kiryanenko/SmartParking-sensor/docs/Приложение Е. Графическая документация.pdf

# ПРИЛОЖЕНИЕ Е

# Графическая документация

# В графическую часть дипломного проекта входят:

1) Цели и задачи системы мониторинга парковочных мест (Рисунок Е.1);
2) Исследование | IoT | технологий | в | сфере | транспортной | инфраструктуры

(Рисунок Е.2);

3) Функциональная схема системы мониторинга парковочных мест (Рисунок Е.3);

# 4) Схема электрическая структурная МК-подсистемы регистрации свободных

парковочных мест (Рисунок Е.4);

# 5) Схема электрическая функциональная модуля контроля парковочного места

(Рисунок Е.5);

# 6) Схема электрическая функциональная МК-подсистемы регистрации свободных

парковочных мест (Рисунок Е.6);

# 7) Спецификация модуля контроля парковочного места на базе PCF8574P

(Рисунок Е.7);

# 8) Схема электрическая принципиальная модуля контроля парковочного места на

базе PCF8574P (Рисунок Е.8);

# 9) Спецификация модуля контроля парковочного места на базе PCF8574AP

(Рисунок Е.9);

# 10) Схема электрическая принципиальная модуля контроля парковочного места на

базе PCF8574AP (Рисунок Е.10);

# 11) Спецификация МК-подсистемы регистрации свободных парковочных мест

(Рисунки Е.11, Е.12);

# 12) Схема электрическая принципиальная МК-подсистемы регистрации свободных

парковочных мест (Рисунок Е.13);

# 13) Диаграмма классов МК-подсистемы регистрации свободных парковочных мест

(Рисунок Е.14);

14) Диаграмма классов вычислительного хаба (Рисунок Е.15);
15) Схема базы данных (Рисунок Е.16);
16) Алгоритм выдачи парковок (Рисунок Е.17);
17) Тестирование системы мониторинга парковочных мест (Рисунок Е.18).

Н.контроль Утв.

Изм. Лист | докум. | Подпись | Дата
Разраб. | Кирьяненко А.В.
Провер. | Попов А.Ю.
Т.контроль
Лит. | Масса | Масштаб
Лист | Листов

Система мониторинга парковочных мест

Цели и задачи

Выпускная квалификационная работа бакалавра

Реценз. | МГТУ им. Н.Э. Баумана группа ИУ6-81

# СИСТЕМА МОНИТОРИНГА ПАРКОВОЧНЫХ МЕСТ

Мобильное приложение | Веб-клиент

База
данных

### Сервер

API-сервисы

Вычислительный хаб | Вычислительный хаб

### МК-подсистема регистрации свободных парковочных мест

### МК-подсистема регистрации свободных парковочных мест

### МК-подсистема регистрации свободных парковочных мест

### МК-подсистема регистрации свободных парковочных мест

Пользователь

Просмотр на карте в режиме реального времени текущих состояний парковок

Фильтрация парковок

Бронирование и оплата парковки

Регистрация

Авторизация

Просмотр совершенных заказов

Бронирование и оплата парковки через терминал оплаты

Получение информации о состоянии парковок по табло индикации

Владелец стоянки

Добавление /
удаление датчика

Добавление / изменение / удаление стоянки

Добавление / изменение / удаление парковочного места

Просмотр совершенных заказов на парковки владельца

Настройка параметров датчика

ЦЕЛИ: Создание программно-аппаратного прототипа системы мониторинга парковочных мест для определения наличия свободных парковок и отображения этих данных пользователям в режиме реального времени.

# ЗАДАЧИ: -Исследование IoT технологий в сфере транспортной инфраструктуры

# -Анализ предметной области -Разработка архитектуры системы

# -Разработка МК-подсистемы регистрации свободных парковочных мест

# -Разработка программной части компонентов системы -Обеспечение качества и надёжности системы

# Рисунок Е.1 – Цели и задачи системы мониторинга парковочных мест

Утв.

Изм. Лист | докум. | Подпись | Дата
Разраб. | Кирьяненко А.В.
Провер. | Попов А.Ю.

Т.контроль

Н.контроль

Лит. | Масса | Масштаб
Лист | Листов

Система мониторинга парковочных мест

Исследование IoT технологий в сфере транспортной инфраструктуры

Выпускная квалификационная работа бакалавра

Реценз. | МГТУ им. Н.Э. Баумана группа ИУ6-81

# Архитектура интернет вещей

Издатель | MQTT-брокер | Подписчик
| CONNECT CONACK CONNECT CONACK SUBSCRIBE SUBACK

## PUBLISH PUBLISH

## PUBLISH PUBLISH

## UNSUBSCRIBE UNSUBACK

# Диаграмма последовательностей MQTT протокола Ethernet, WiFi, 3G, 4G

## Сетевой сервер

## Сервер приложений

## Конечное устройство

## Конечное устройство

Конечное устройство | Модуляция LoRa

## Шлюз

## Конечное устройство

Архитектура сети LoRaWAN | Преимущества LoRaWAN: -Большая дальность передачи 10 – 15 км. -Низкое энергопотребление. -Высокая проникающая способность. -Высокая масштабируемость. -Отсутствие необходимости получения частотного разрешения. | Недостатки LoRaWAN: -Низкая пропускная способность от 0,1 кбит/с до 10 кбит/с. -Большая задержка передачи данных от 1 с до 10 с. -Отсутствие единого стандарта. -Риски зашумленности. -Ограничение мощности сигнала.

# Рисунок Е.2 – Исследование IoT технологий в сфере транспортной инфраструктуры

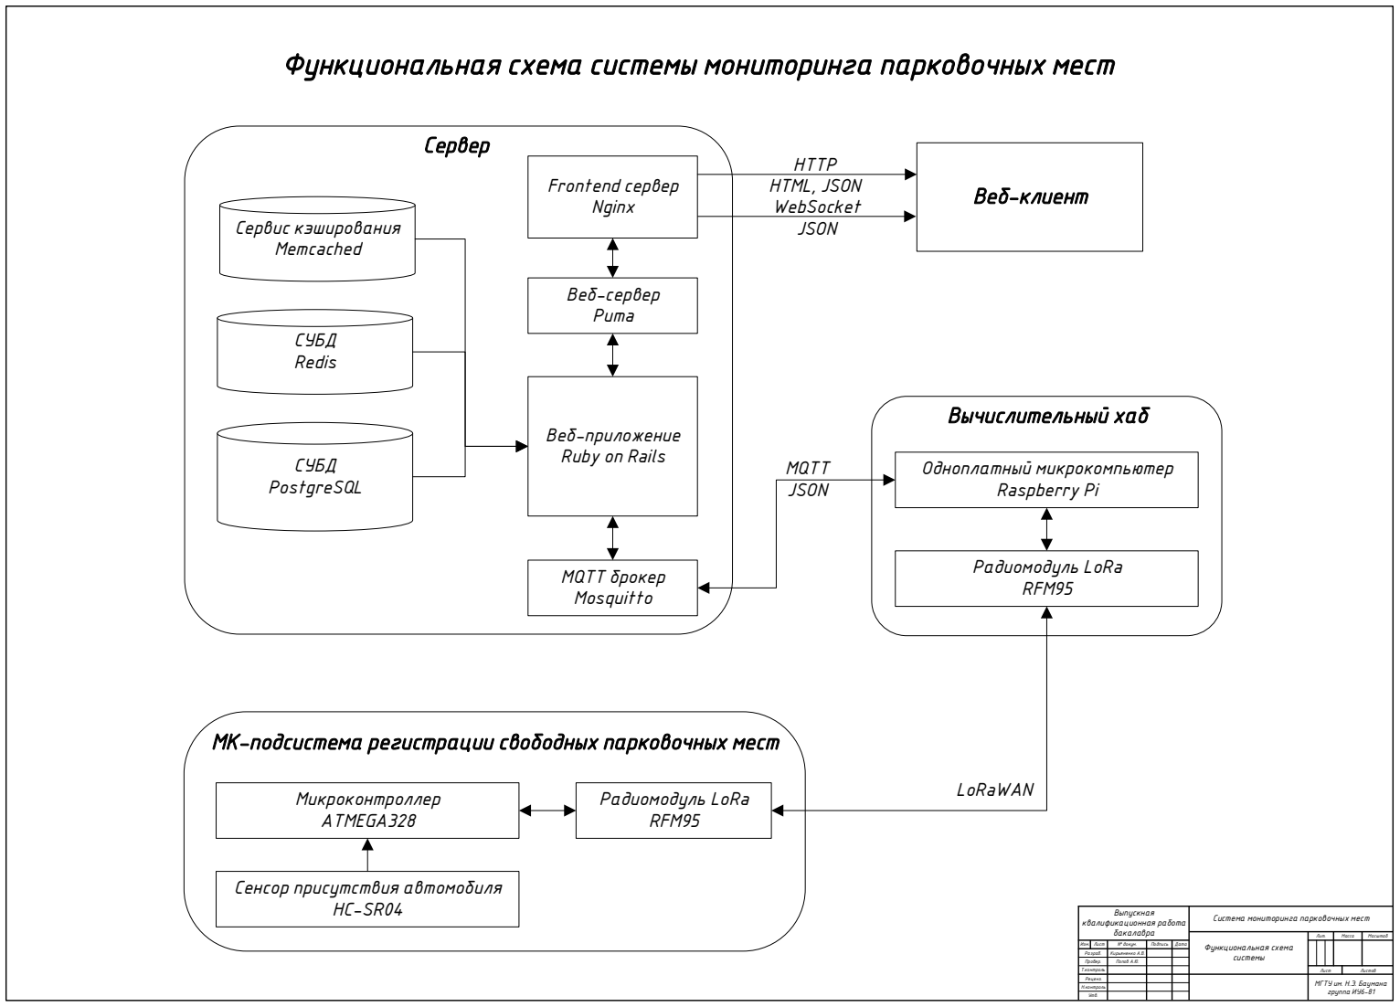
[picture p59: figure]
Н.контроль Утв.; Т.контроль; Провер.; Попов А.Ю.; Разраб.; Кирьяненко А.В.; Изм. Лист; докум.; Подпись; Дата; Лит.; Масса; Масштаб; Лист; Листов; Система мониторинга парковочных мест; Функциональная схема системы; Выпускная квалификационная работа бакалавра; Frontend сервер Nginx; Веб-сервер Puma; Веб-приложение Ruby on Rails СУБД; PostgreSQL; СУБД Redis; Сервис кэширования Memcached; MQTT брокер Mosquitto; Веб-клиент; HTTP HTML, JSON WebSocket; JSON; Сервер; Одноплатный микрокомпьютер Raspberry Pi; Радиомодуль LoRa RFM95; Вычислительный хаб; MQTT JSON; Микроконтроллер ATMEGA328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

Реценз. | МГТУ им. Н.Э. Баумана группа ИУ6-81

# МК-подсистема регистрации свободных парковочных мест

# Функциональная схема системы мониторинга парковочных мест

# Рисунок Е.3 – Функциональная схема системы мониторинга парковочных мест

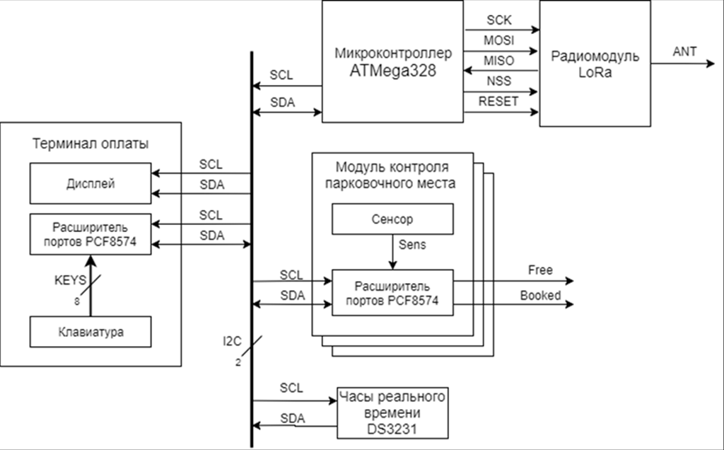
[picture p60: figure]

Утв.

Изм. | Лист | докум. | Подпись | Дата
Разраб. | | Кирьяненко А.В.
Провер. | | Попов А.Ю.

### Т.контроль

Н.контроль | | Бауман Ю.И.
Лит. | Масса | Масштаб
Лист 1 | Листов 1

# Система мониторинга парковочных мест

# МК-подсистема регистрации свободных парковочных мест

# Выпускная квалификационная работа бакалавра

Реценз. | МГТУ им. Н.Э. Баумана
| группа ИУ6-81
| Формат А4

# Схема электрическая структурная

Рисунок Е.4 – Схема электрическая структурная МК-подсистемы регистрации свободных парковочных мест

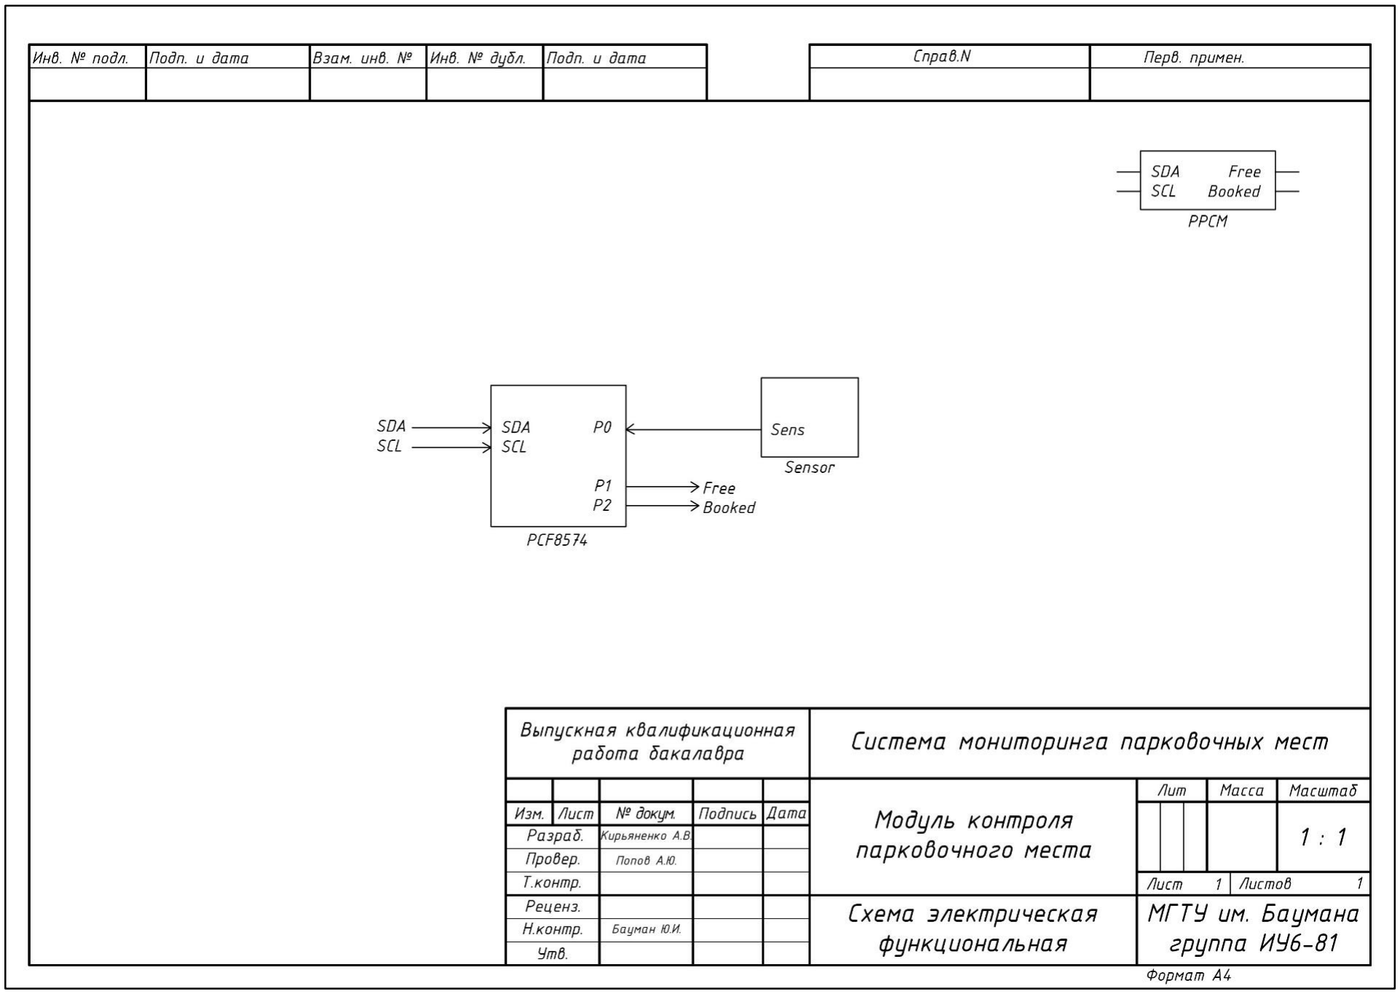
[picture p61: figure]

# Рисунок Е.5 – Схема электрическая функциональная модуля контроля парковочного места

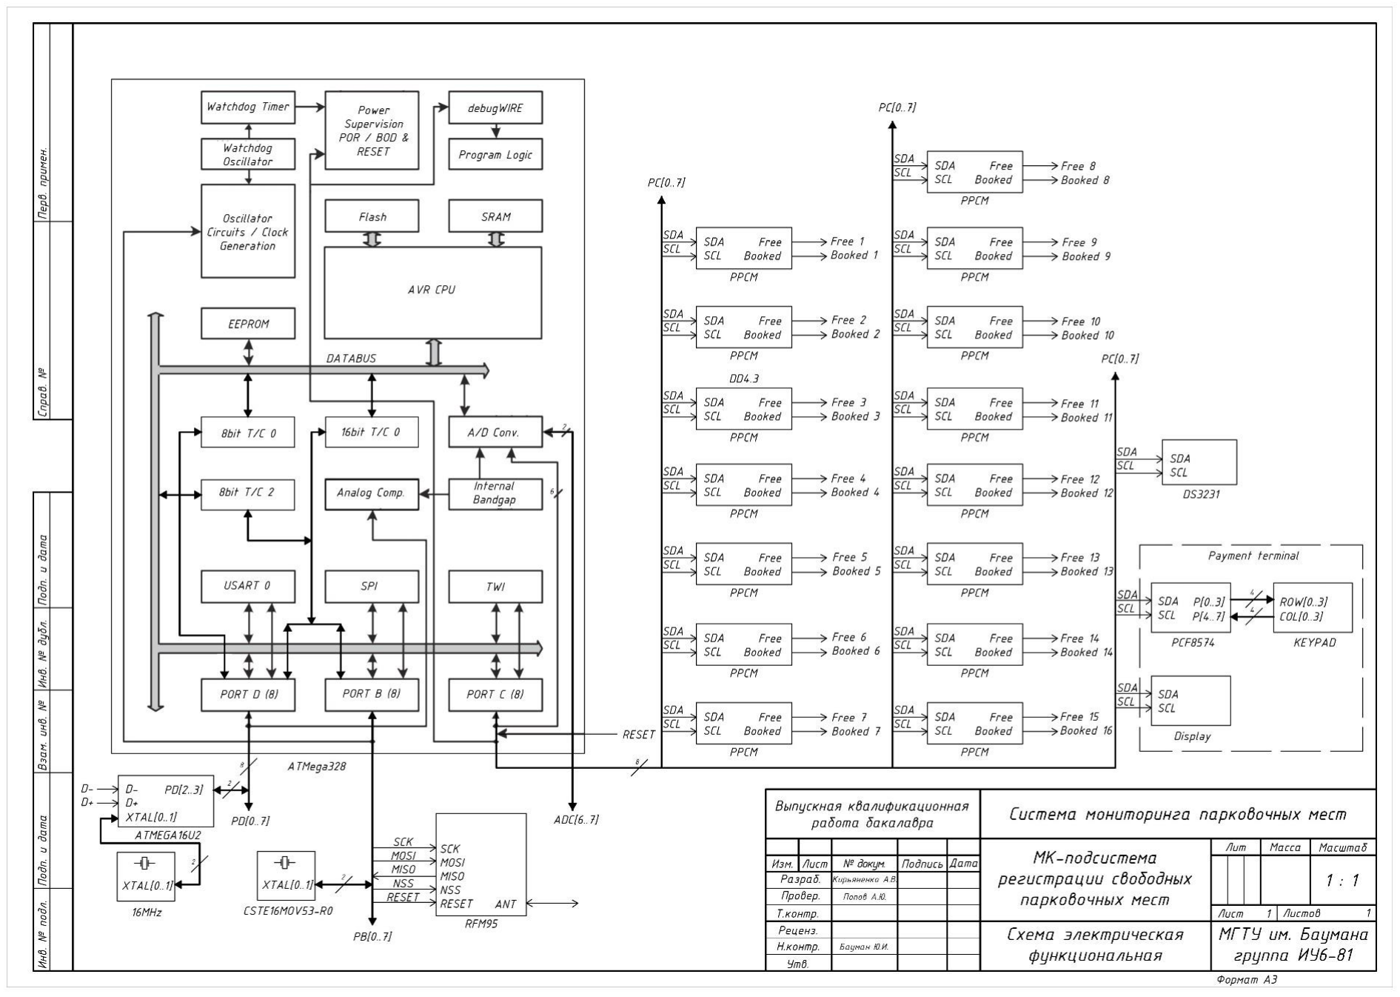
[picture p62: figure]

Рисунок Е.6 – Схема электрическая функциональная МК-подсистемы регистрации свободных парковочных мест

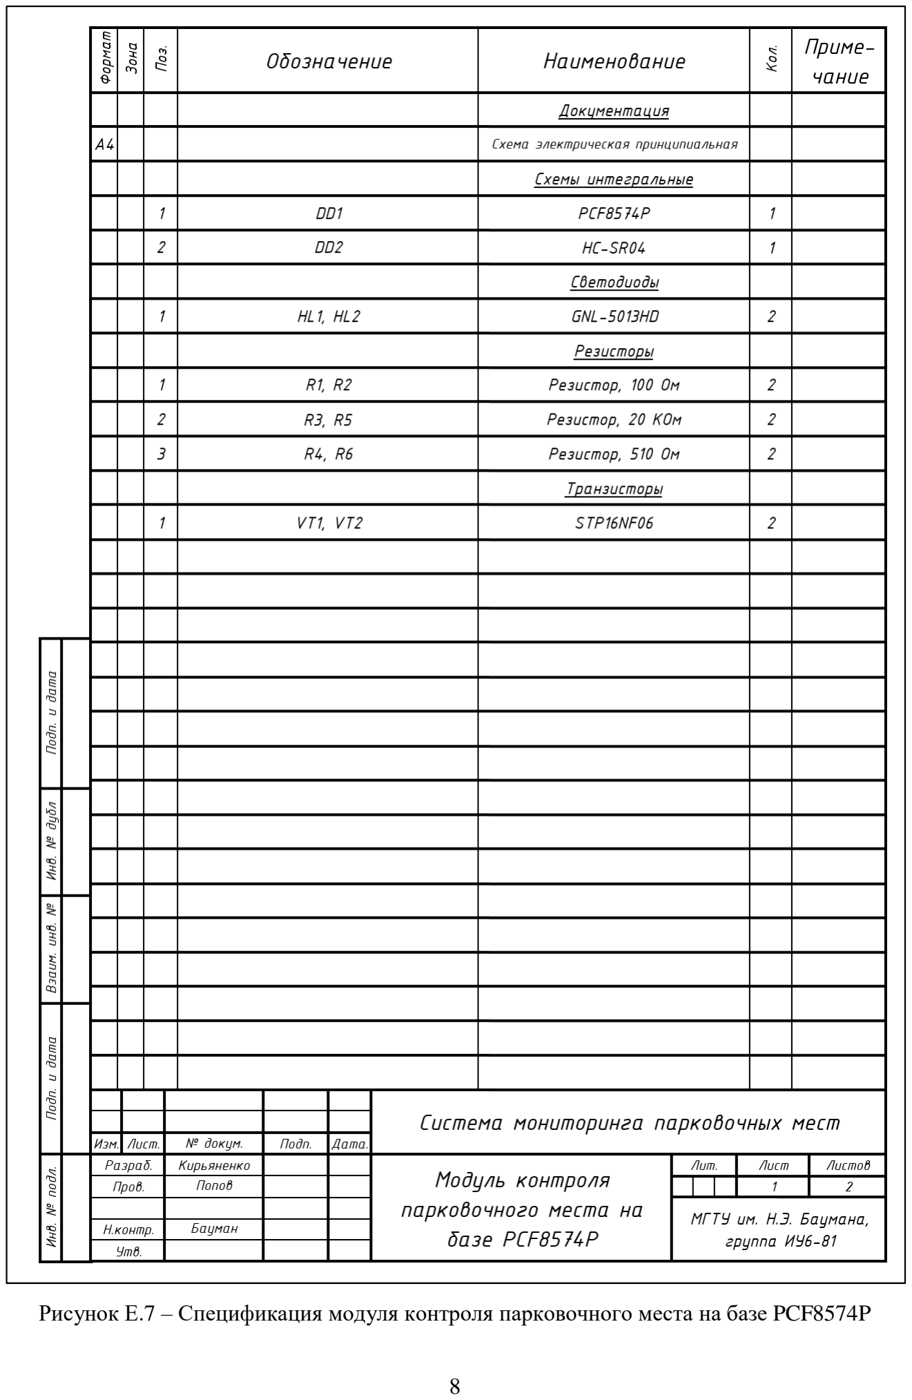
[picture p63: page 8]

# Рисунок Е.7 – Спецификация модуля контроля парковочного места на базе PCF8574P

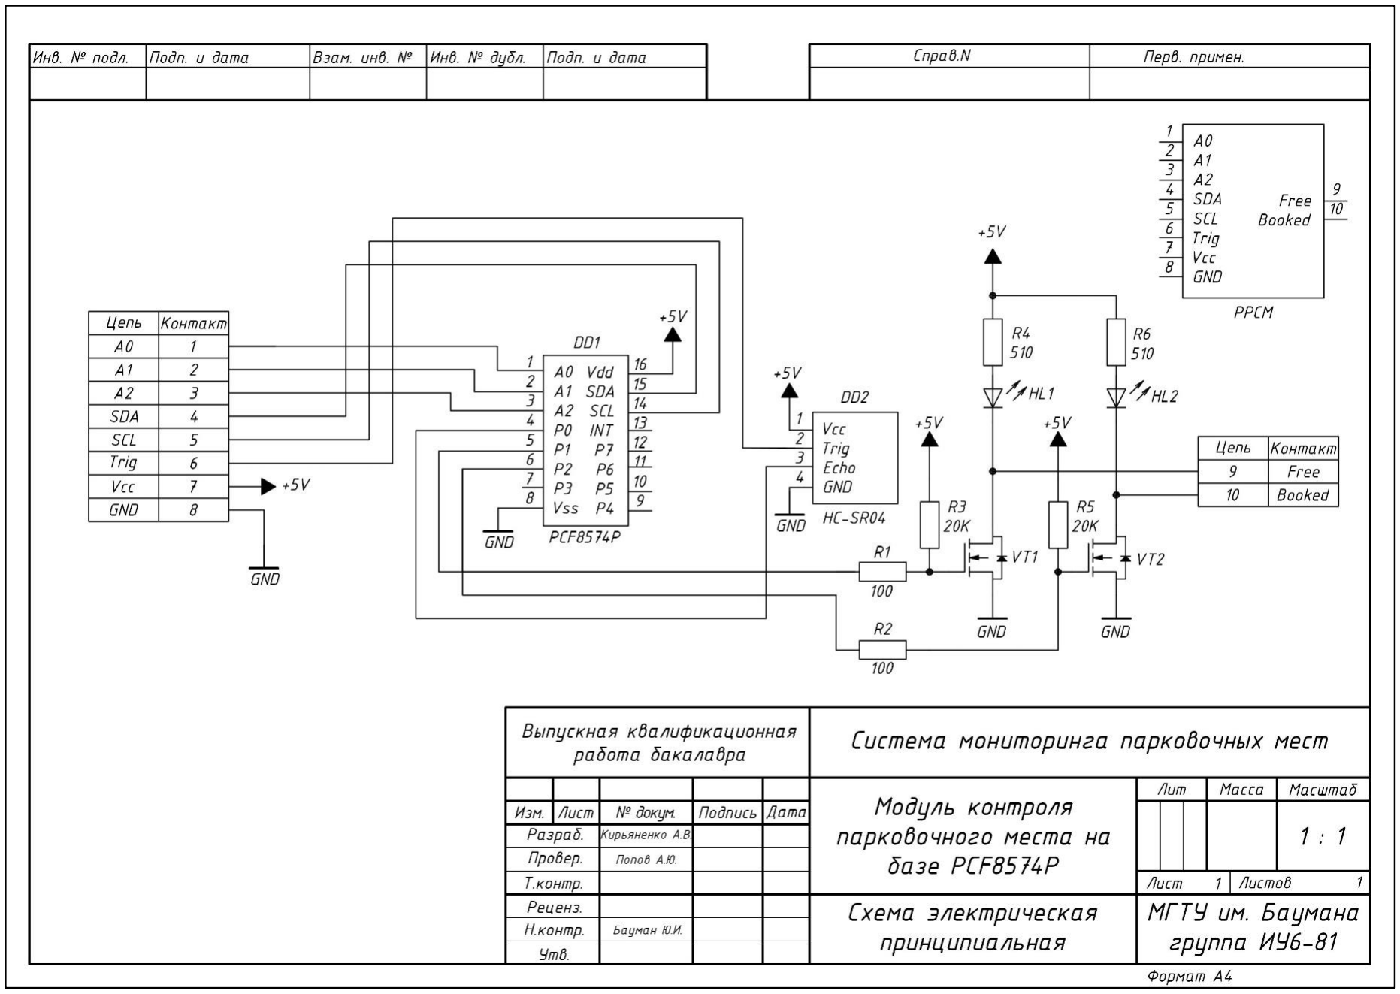
[picture p64: figure]

Рисунок Е.8 – Схема электрическая принципиальная модуля контроля парковочного места на базе PCF8574P

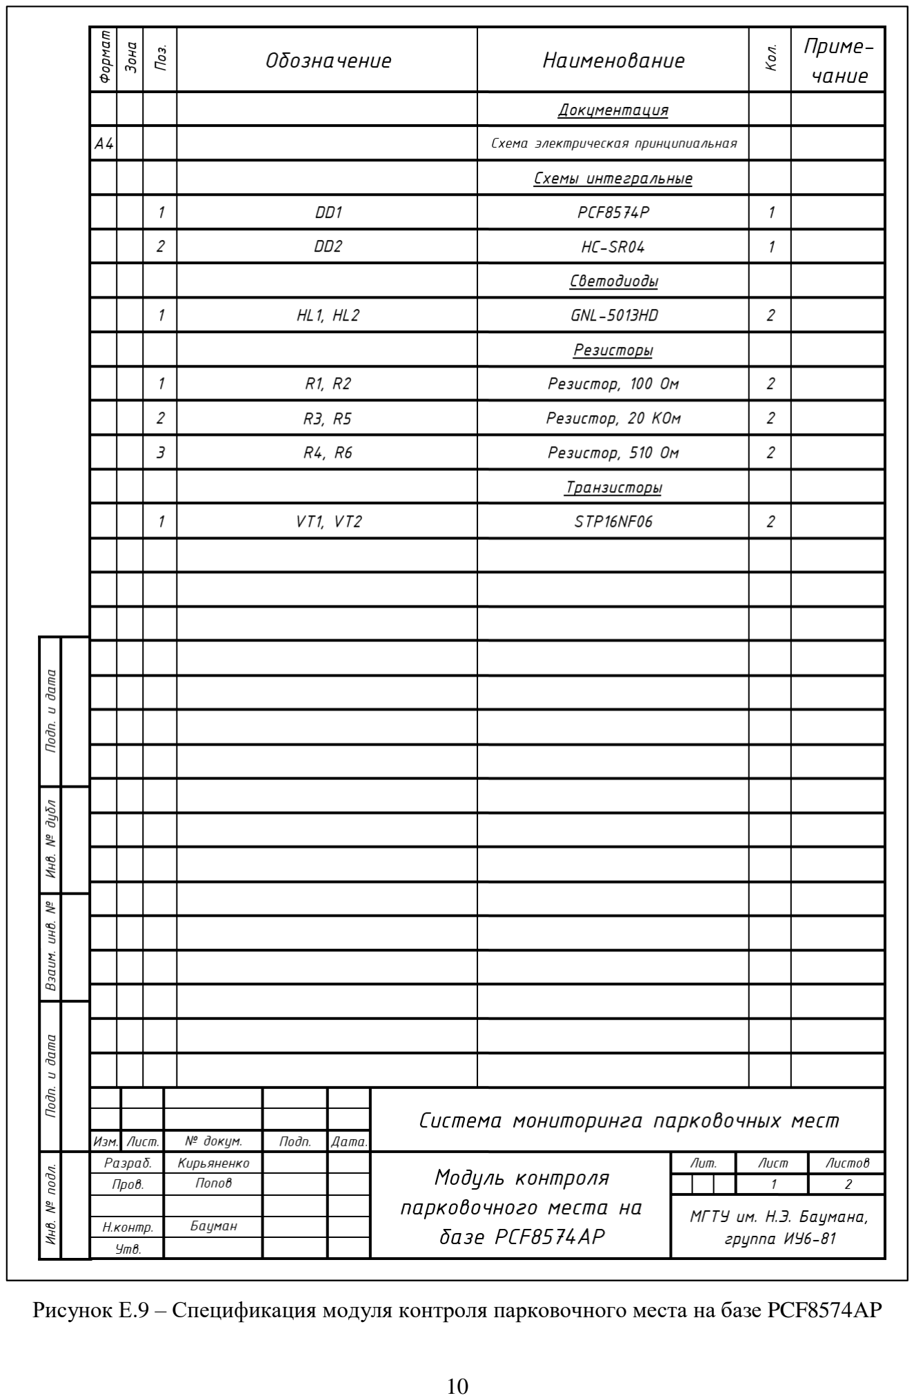
[picture p65: page 10]

# Рисунок Е.9 – Спецификация модуля контроля парковочного места на базе PCF8574АP

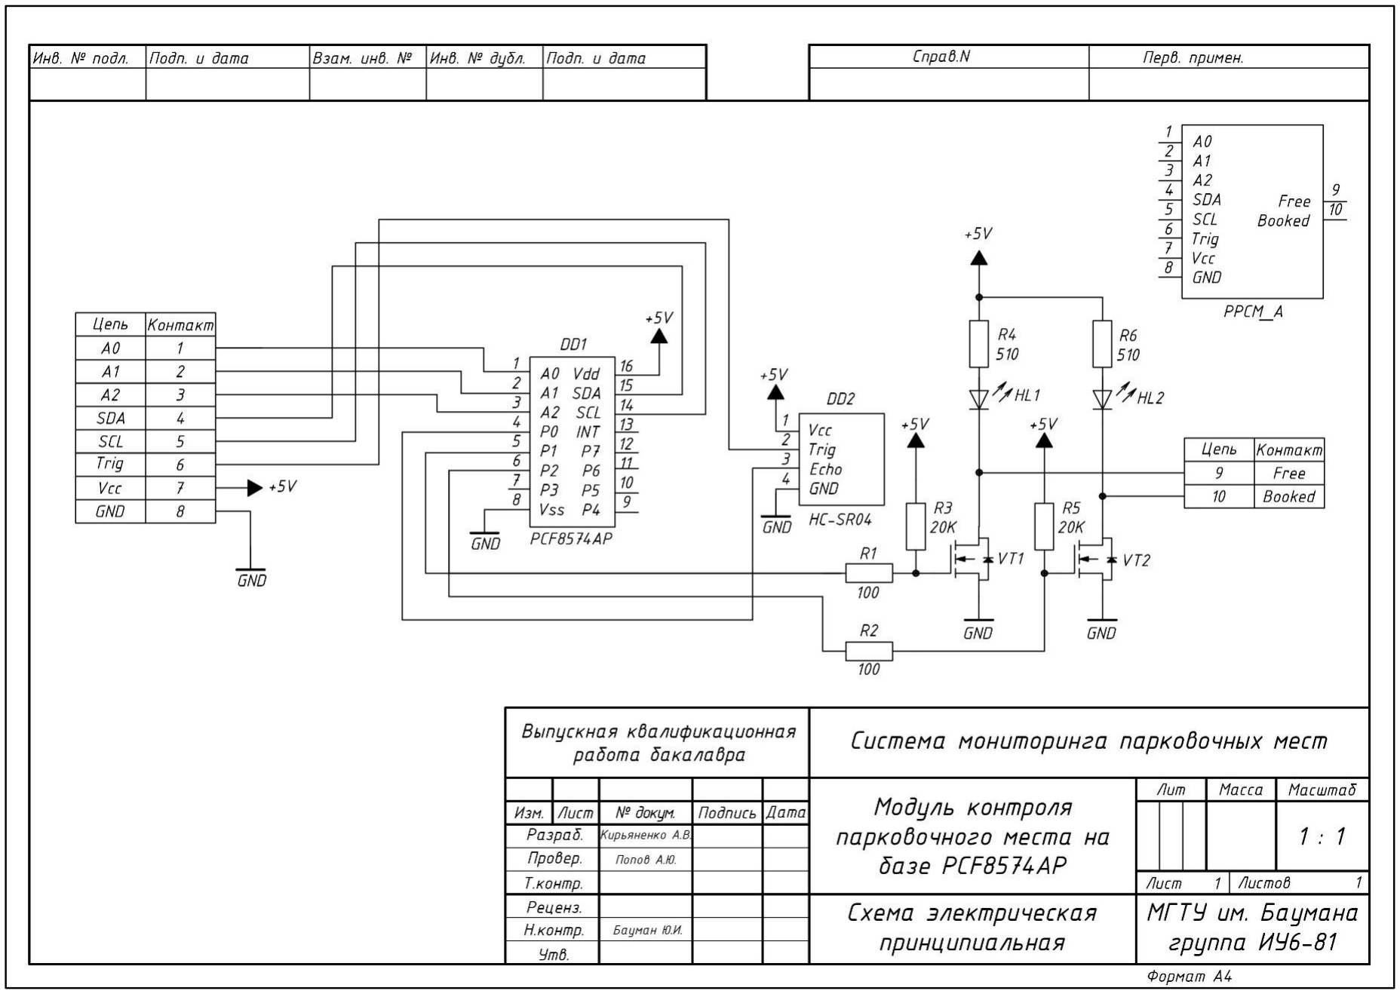
[picture p66: figure]

Рисунок Е.10 – Схема электрическая принципиальная модуля контроля парковочного места на базе PCF8574AP

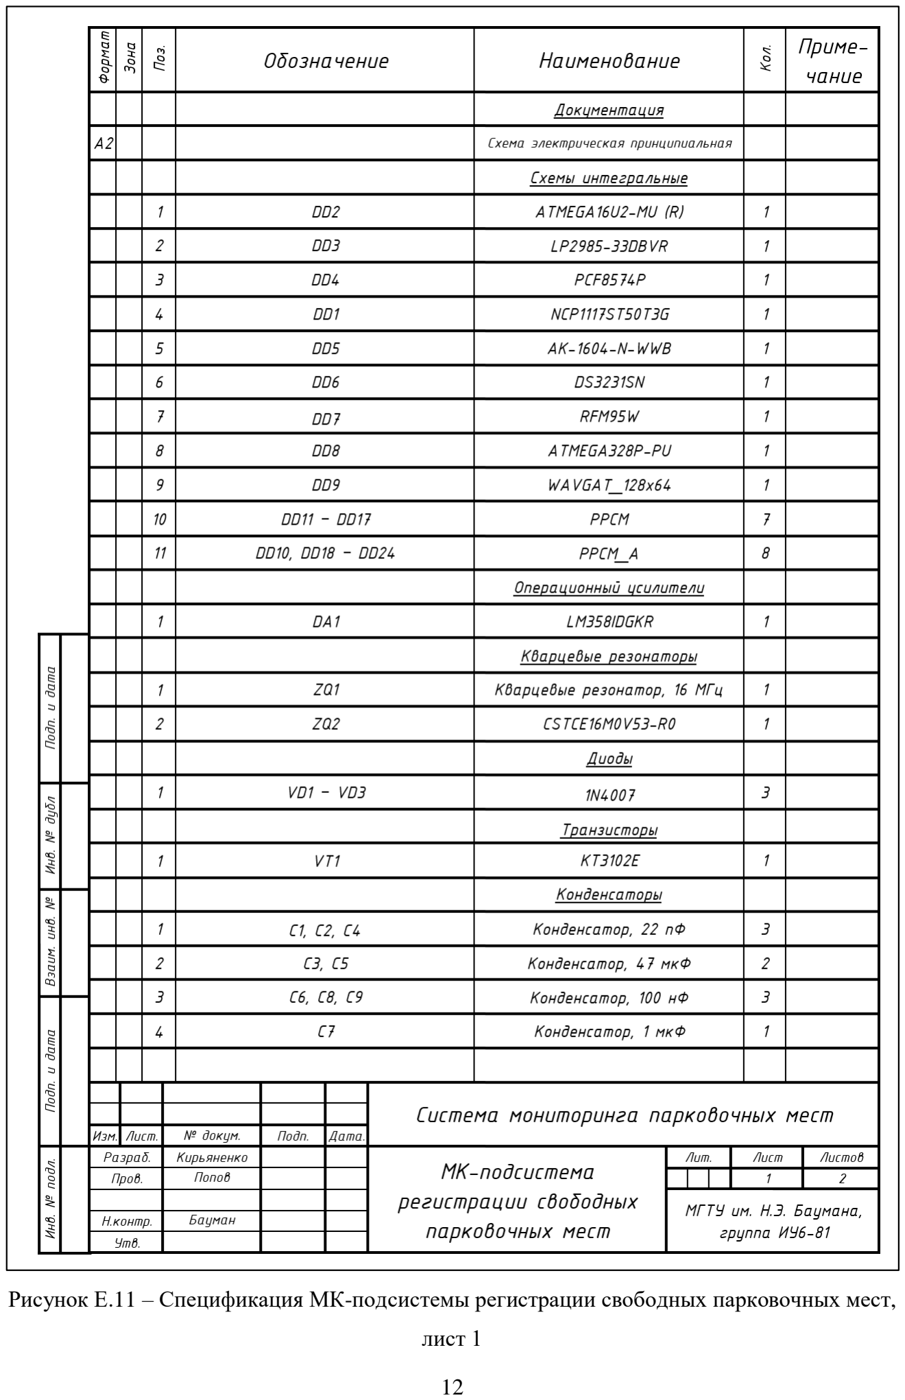
[picture p67: page 12]

Рисунок Е.11 – Спецификация МК-подсистемы регистрации свободных парковочных мест,

# лист 1

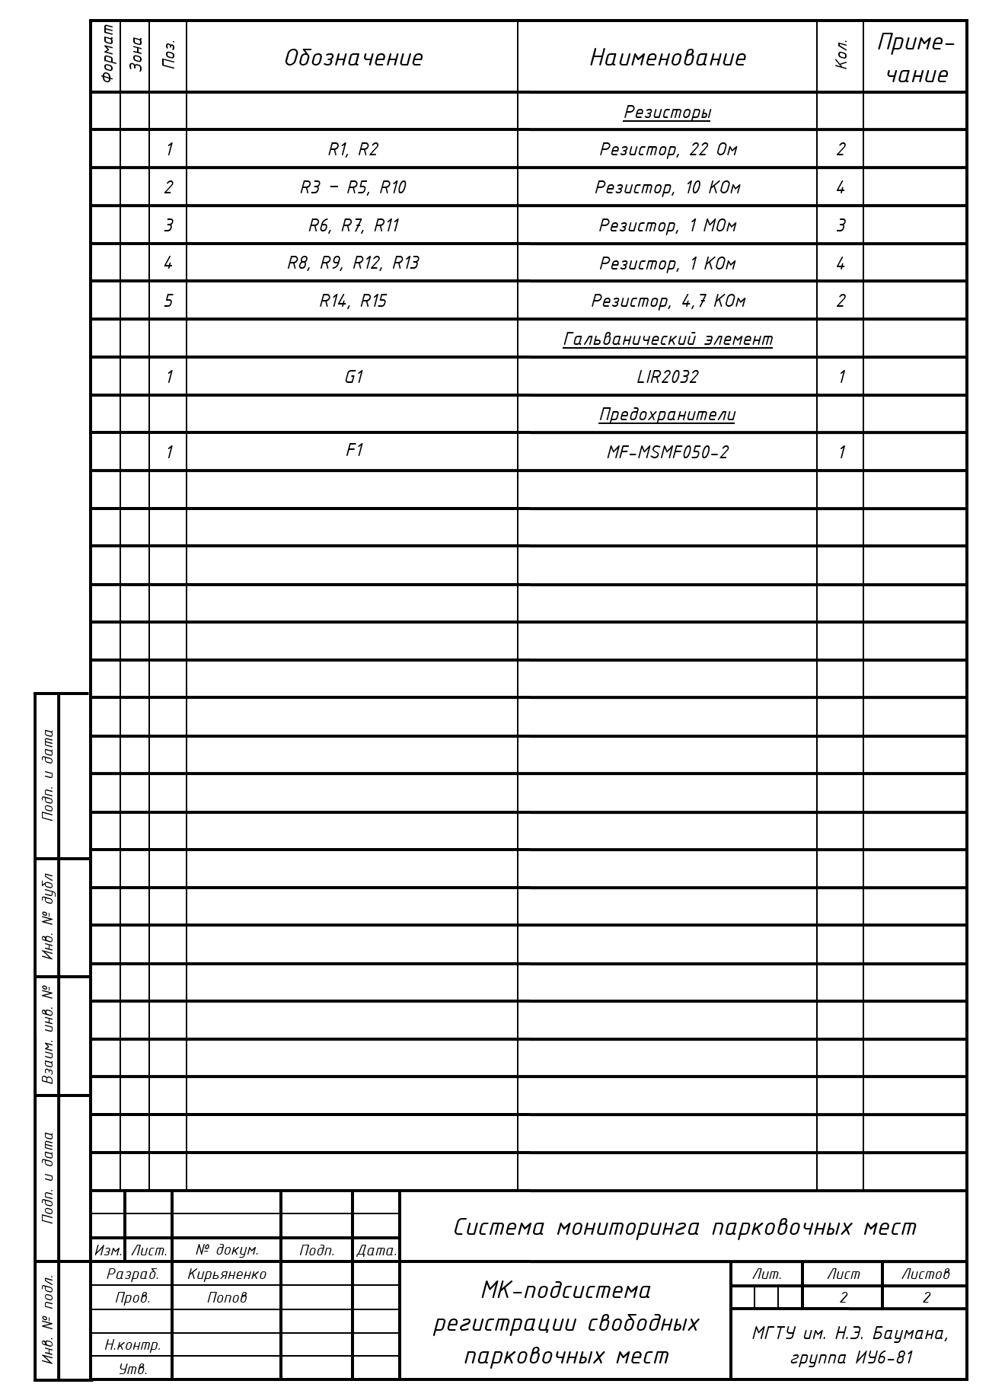
[picture p68: page 13]

Рисунок Е.12 – Спецификация МК-подсистемы регистрации свободных парковочных мест,

# лист 2

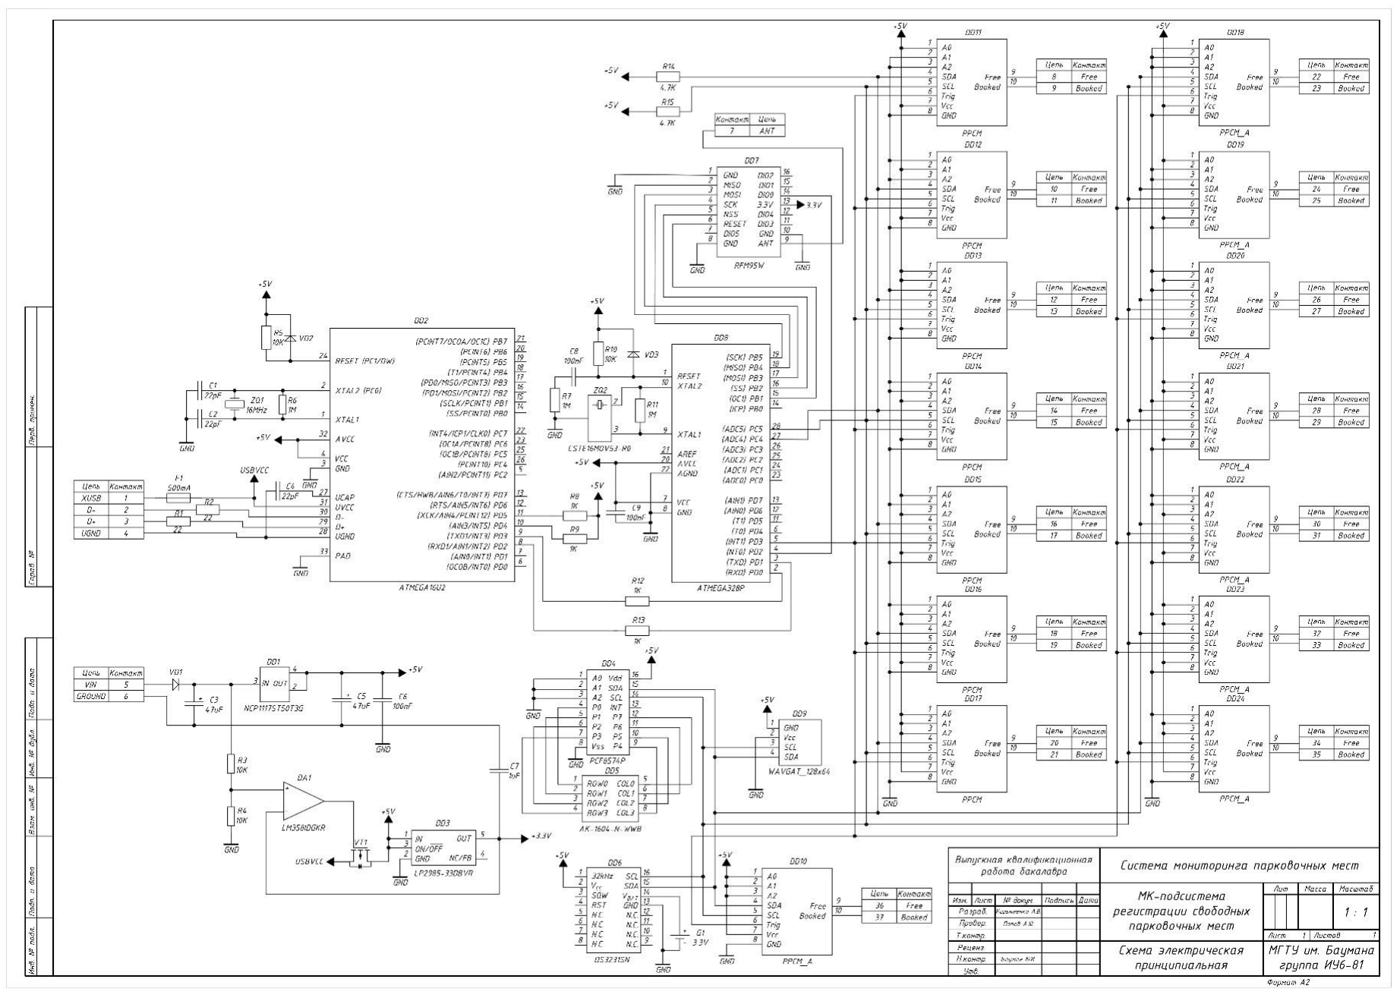
[picture p69: figure]

Рисунок Е.13 – Схема электрическая принципиальная МК-подсистемы регистрации свободных парковочных мест

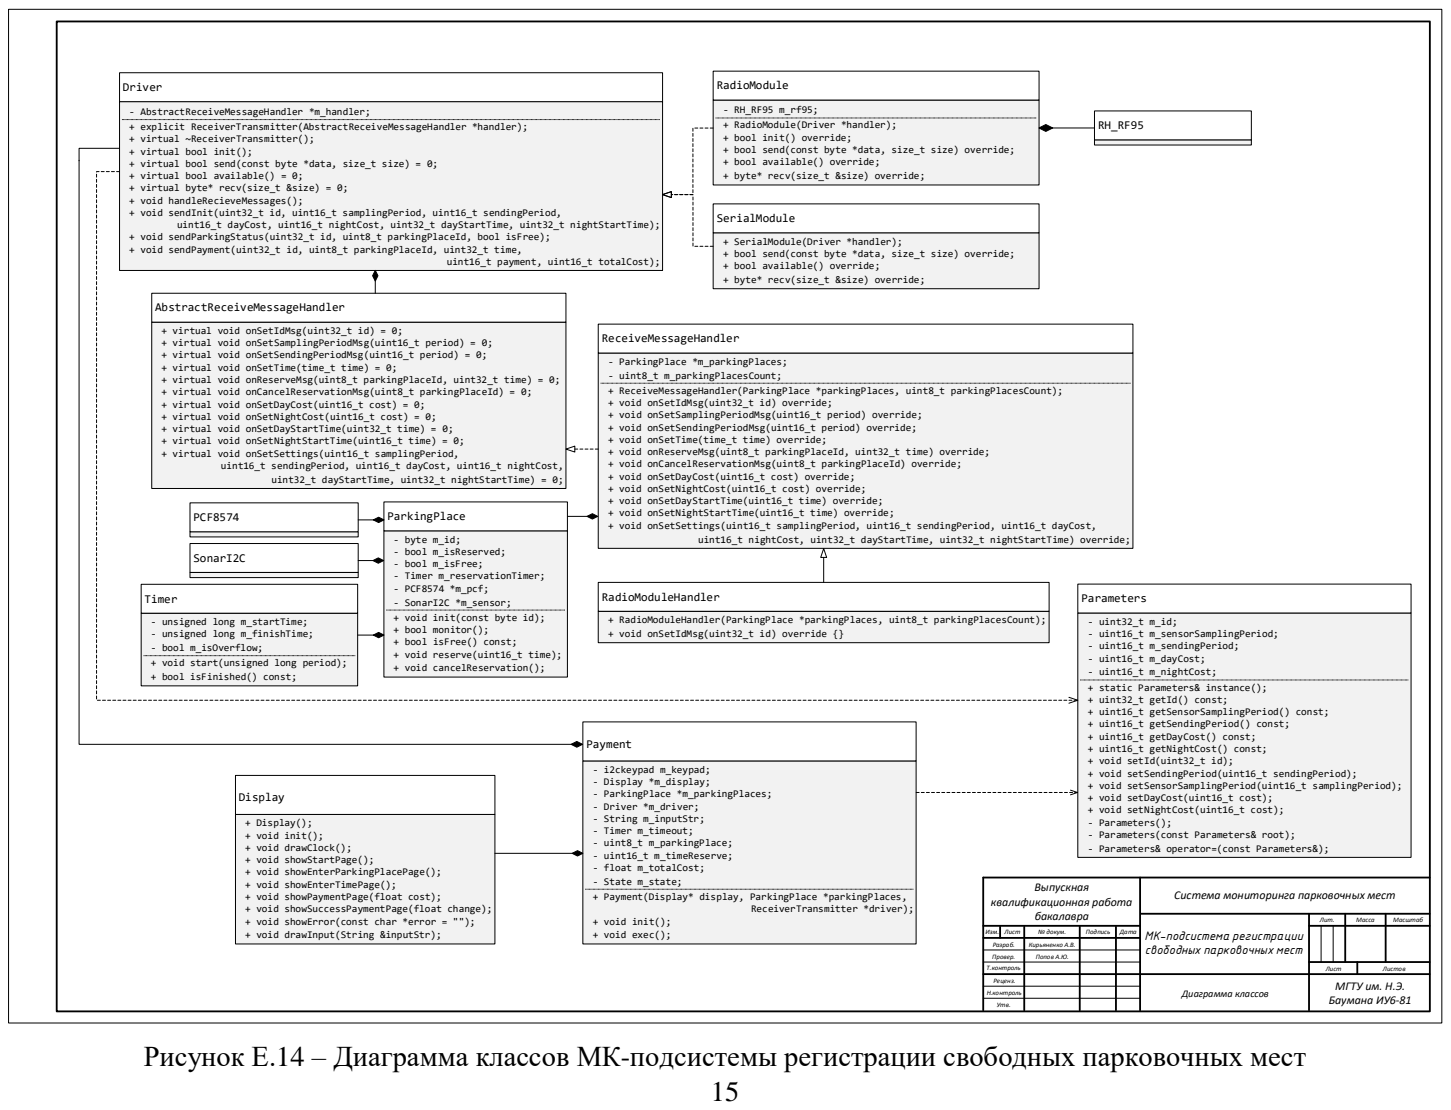
[picture p70: page 15]
Driver; uint16_t payment, uint16_t totalCost);; AbstractReceiveMessageHandler; uint32_t dayStartTime, uint32_t nightStartTime) = 0;; RadioModule; SerialModule; ReceiveMessageHandler; RadioModuleHandler; ParkingPlace; Timer; PCF8574; SonarI2C; Parameters; Payment; - i2ckeypad m_keypad; - Display *m_display; - ParkingPlace *m_parkingPlaces; - Driver *m_driver; - String m_inputStr; - Timer m_timeout; - uint8_t m_parkingPlace; - uint16_t m_timeReserve; - float m_totalCost; - State m_state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

- AbstractReceiveMessageHandler *m_handler;
+ explicit ReceiverTransmitter(AbstractReceiveMessageHandler *handler);
+ virtual ~ReceiverTransmitter();
+ virtual bool init();
+ virtual bool send(const byte *data, size_t size) = 0;
+ virtual bool available() = 0;
+ virtual byte* recv(size_t &size) = 0;
+ void handleRecieveMessages();
+ void sendInit(uint32_t id, uint16_t samplingPeriod, uint16_t sendingPeriod,

+ RadioModule(Driver *handler);
+ bool init() override;
+ bool send(const byte *data, size_t size) override;
+ bool available() override;
+ byte* recv(size_t &size) override;

uint16_t dayCost, uint16_t nightCost, uint32_t dayStartTime, uint32_t nightStartTime);

+ void sendParkingStatus(uint32_t id, uint8_t parkingPlaceId, bool isFree);
+ void sendPayment(uint32_t id, uint8_t parkingPlaceId, uint32_t time,

+ SerialModule(Driver *handler);

+ virtual void onSetIdMsg(uint32_t id) = 0;
+ virtual void onSetSamplingPeriodMsg(uint16_t period) = 0;
+ virtual void onSetSendingPeriodMsg(uint16_t period) = 0;
+ virtual void onSetTime(time_t time) = 0;
+ virtual void onReserveMsg(uint8_t parkingPlaceId, uint32_t time) = 0;
+ virtual void onCancelReservationMsg(uint8_t parkingPlaceId) = 0;
+ virtual void onSetDayCost(uint16_t cost) = 0;
+ virtual void onSetNightCost(uint16_t cost) = 0;
+ virtual void onSetDayStartTime(uint32_t time) = 0;
+ virtual void onSetNightStartTime(uint16_t time) = 0;
+ virtual void onSetSettings(uint16_t samplingPeriod,

- ParkingPlace *m_parkingPlaces;
- uint8_t m_parkingPlacesCount;
+ ReceiveMessageHandler(ParkingPlace *parkingPlaces, uint8_t parkingPlacesCount);
+ void onSetIdMsg(uint32_t id) override;
+ void onSetSamplingPeriodMsg(uint16_t period) override;
+ void onSetSendingPeriodMsg(uint16_t period) override;
+ void onSetTime(time_t time) override;
+ void onReserveMsg(uint8_t parkingPlaceId, uint32_t time) override;
+ void onCancelReservationMsg(uint8_t parkingPlaceId) override;
+ void onSetDayCost(uint16_t cost) override;
+ void onSetNightCost(uint16_t cost) override;
+ void onSetDayStartTime(uint16_t time) override;
+ void onSetNightStartTime(uint16_t time) override;
+ void onSetSettings(uint16_t samplingPeriod, uint16_t sendingPeriod, uint16_t dayCost,

uint16_t sendingPeriod, uint16_t dayCost, uint16_t nightCost,

- byte m_id;
- bool m_isReserved;
- bool m_isFree;
- Timer m_reservationTimer;
- PCF8574 *m_pcf;
- SonarI2C *m_sensor;
+ void init(const byte id);
+ bool monitor();
+ bool isFree() const;
+ void reserve(uint16_t time);
+ void cancelReservation();

uint16_t nightCost, uint32_t dayStartTime, uint32_t nightStartTime) override;

- unsigned long m_startTime;
- unsigned long m_finishTime;
- bool m_isOverflow;
+ void start(unsigned long period);
+ bool isFinished() const;

+ RadioModuleHandler(ParkingPlace *parkingPlaces, uint8_t parkingPlacesCount);
+ void onSetIdMsg(uint32_t id) override {}

- uint32_t m_id;
- uint16_t m_sensorSamplingPeriod;
- uint16_t m_sendingPeriod;
- uint16_t m_dayCost;
- uint16_t m_nightCost;
+ static Parameters& instance();
+ uint32_t getId() const;
+ uint16_t getSensorSamplingPeriod() const;
+ uint16_t getSendingPeriod() const;
+ uint16_t getDayCost() const;
+ uint16_t getNightCost() const;
+ void setId(uint32_t id);
+ void setSendingPeriod(uint16_t sendingPeriod);
+ void setSensorSamplingPeriod(uint16_t samplingPeriod);
+ void setDayCost(uint16_t cost);
+ void setNightCost(uint16_t cost);
- Parameters();
- Parameters(const Parameters& root);
- Parameters& operator=(const Parameters&);

+ Display();
+ void init();
+ void drawClock();
+ void showStartPage();
+ void showEnterParkingPlacePage();
+ void showEnterTimePage();
+ void showPaymentPage(float cost);
+ void showSuccessPaymentPage(float change);
+ void showError(const char *error = "");
+ void drawInput(String &inputStr);

Система мониторинга парковочных мест

Изм. | Лист | докум. | Подпись | Дата
Разраб. | | Кирьяненко А.В.
Провер. | | Попов А.Ю.
Т.контроль

МК-подсистема регистрации
свободных парковочных мест

Н.контроль

Рисунок Е.14 – Диаграмма классов МК-подсистемы регистрации свободных парковочных мест

Утв.

Изм. | Лист | докум. | Подпись | Дата
Разраб. | | Кирьяненко
Провер. | | Попов

Т.контроль

Н.контроль

Лит. | Масса | Масштаб
Лист | Листов

Система мониторинга парковочных мест Выпускная квалификационная работа
бакалавра
Реценз. | МГТУ им. Н.Э. Баумана ИУ6-81

Driver

- AbstractReceiveMessageHandler *m_handler;
- QList<quint32> m_sensors;
+ explicit Driver(QList<quint32> &sensors,
AbstractReceiveMessageHandler *handler = new AbstractReceiveMessageHandler(), QObject *parent = 0); + virtual ~Driver();
+ virtual bool send(QByteArray data) = 0;
+ virtual bool available() = 0;
+ virtual QByteArray recv() = 0;
+ void setHandler(AbstractReceiveMessageHandler *handler);
+ void handleRecieveMessages();
+ void sendSetId(quint32 sensorId, quint32 newId);
+ void sendSetSensorSamplingPeriod(quint32 sensorId, quint16 samplingPeriod);
+ void sendSetSendingPeriod(quint32 sensorId, quint16 sendingPeriod);
+ void sendSetSettings(quint32 sensorId, quint16 samplingPeriod, quint16 sendingPeriod, quint16 dayCost, quint16 nightCost, quint32 dayStartTime, quint32 nightStartTime); + void sendReserve(quint32 sensorId, quint16 parkingPlaceId, quint32 time);
+ void sendCancelReservation(quint32 sensorId, quint8 parkingPlaceId);

AbstractReceiveMessageHandler

+ AbstractReceiveMessageHandler(QObject *parent = 0);
+ virtual ~AbstractReceiveMessageHandler();
+ virtual void onRecv(QByteArray data) {}
+ virtual void onParkingStatus(quint32 id, quint8 place, bool isFree) {}
+ virtual void onInit(quint32 id, quint16 samplingPeriod, quint16 sendingPeriod, quint16 dayCost, quint16 nightCost, quint32 dayStartTime, quint32 nightStartTime) {} + virtual void onPayment(quint32 id, quint8 place, quint32 bookedTime,
quint16 payment, quint16 totalCost) {} + virtual void onBook(quint32 sensor, quint8 place, quint32 bookedTime) {}
+ virtual void onSetSensorSettings(quint32 sensor, quint16 samplingPeriod, quint16 sendingPeriod, quint16 dayCost, quint16 nightCost, quint32 dayStartTime, quint32 nightStartTime) {}

LoRaConnection

- RH_RF95 m_rf95;
+ explicit LoRaConnection(QList<quint32> &sensors, int frequency, uint16_t timeout, AbstractReceiveMessageHandler *handler = new AbstractReceiveMessageHandler()); + ~LoRaConnection();
+ bool send(QByteArray data) override;
+ bool available() override;
+ QByteArray recv() override;

SerialConnection

+ explicit SerialConnection(QList<quint32> &sensors, QString portName, qint32 baudRate = QSerialPort::Baud9600, AbstractReceiveMessageHandler *handler = new AbstractReceiveMessageHandler(), QObject *parent = 0); + ~SerialConnection();
+ bool send(QByteArray data) override;
+ bool available() override;
+ QByteArray recv() override;

RH_RF95

ReceiveMessageHandler

- QList<Server*> m_servers;
- Driver *m_driver;
+ ReceiveMessageHandler(QList<Server*> &servers, Driver *driver, QObject *parent = 0); + ~ReceiveMessageHandler();
+ void onRecv(QByteArray data) override;
+ void onParkingStatus(quint32 id, quint8 place, bool isFree) override;
+ void onInit(quint32 id, quint16 samplingPeriod, quint16 sendingPeriod, quint16 dayCost,
quint16 nightCost, quint32 dayStartTime, quint32 nightStartTime) override; + void onPayment(quint32 id, quint8 place, quint32 bookedTime, quint16 payment, quint16 totalCost) override; + void onBook(quint32 sensor, quint8 place, quint32 bookedTime) override;
+ void onSetSensorSettings(quint32 sensor, quint16 samplingPeriod, quint16 sendingPeriod, quint16 dayCost, quint16 nightCost, quint32 dayStartTime, quint32 nightStartTime) override;
- QSerialPort m_serial;

Server

- QMqttClient *m_mqtt;
- AbstractReceiveMessageHandler *m_handler;
- QList<quint32> m_sensors;
+ Server(QString host, quint16 mqtt_port, QString mqttUsername, QString mqttPwd, QString login, QString pwd, QList<quint32> sensors, AbstractReceiveMessageHandler *handler = new AbstractReceiveMessageHandler(), QObject *parent = 0); + ~Server();
+ void setHandler(AbstractReceiveMessageHandler *handler);
+ void sendParkingStatus(qint64 id, quint8 place, bool isFree);
+ void sendInit(qint64 id, quint16 samplingPeriod, quint16 sendingPeriod, quint16 dayCost, quint16 nightCost, qint64 dayStartTime, qint64 nightStartTime); + void sendPayment(qint64 id, quint8 place, qint64 bookedTime, quint16 payment, quint16 totalCost);

Worker

- Driver *m_driver;
+ Worker(QSettings *settngs, QObject *parent = 0); + ~Worker();
+ void run();

Вычислительный хаб

Бауман | Диаграмма классов

# Рисунок Е.15 – Диаграмма классов вычислительного хаба

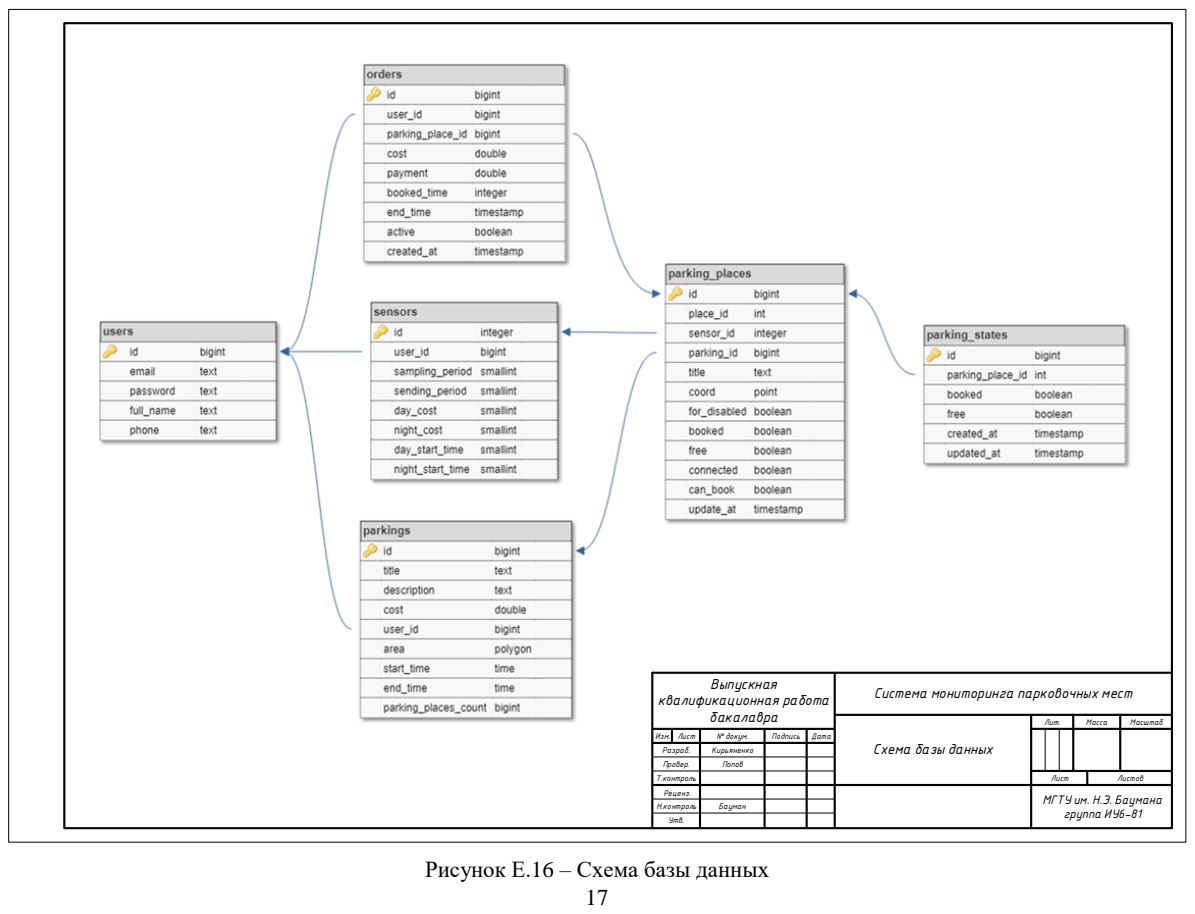
[picture p71: page 17]

Утв.

Изм. | Лист | докум. | Подпись | Дата
Разраб. | | Кирьяненко
Провер. | | Попов

Т.контроль

Н.контроль | | Бауман
Лит. | Масса | Масштаб
Лист | Листов

## Система мониторинга парковочных мест

## Схема базы данных

## Выпускная квалификационная работа бакалавра

Реценз. | МГТУ им. Н.Э. Баумана
| группа ИУ6-81

# Рисунок Е.16 – Схема базы данных

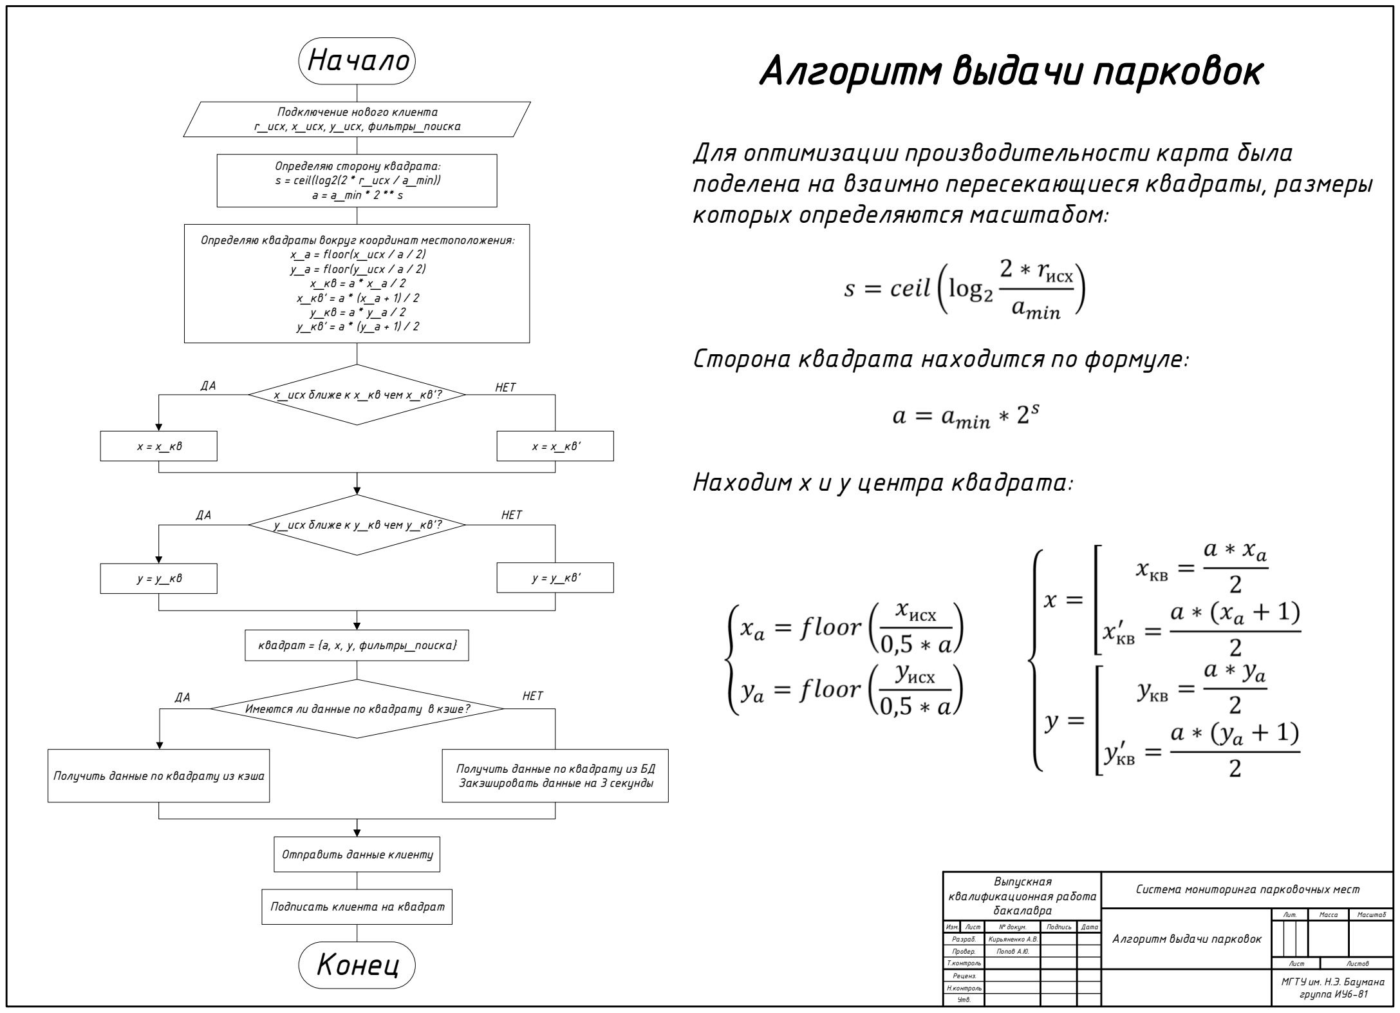
[picture p72: figure]
Н.контроль; Утв.; Т.контроль; Провер.; Попов А.Ю.; Разраб.; Кирьяненко А.В.; Изм.; Лист; докум.; Подпись; Дата; Лит.; Масса; Масштаб; Листов; Система мониторинга парковочных мест; Алгоритм выдачи парковок; Выпускная квалификационная работа бакалавра; Реценз.; МГТУ им. Н.Э. Баумана; группа ИУ6-81; Начало; Определяю сторону квадрата: s = ceil(log2(2 * r_исх / a_min)) a = a_min * 2 ** s; Подключение нового клиента r_исх, x_исх, y_исх, фильтры_поиска; НЕТ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

Получить данные по квадрату из кэша | Получить данные по квадрату из БД

# Для оптимизации производительности карта была поделена на взаимно пересекающиеся квадраты, размеры

# Рисунок Е.17 – Алгоритм выдачи парковок

# Принципиальная схема сети, развернутой на Google Cloud

# График RPS на серверах

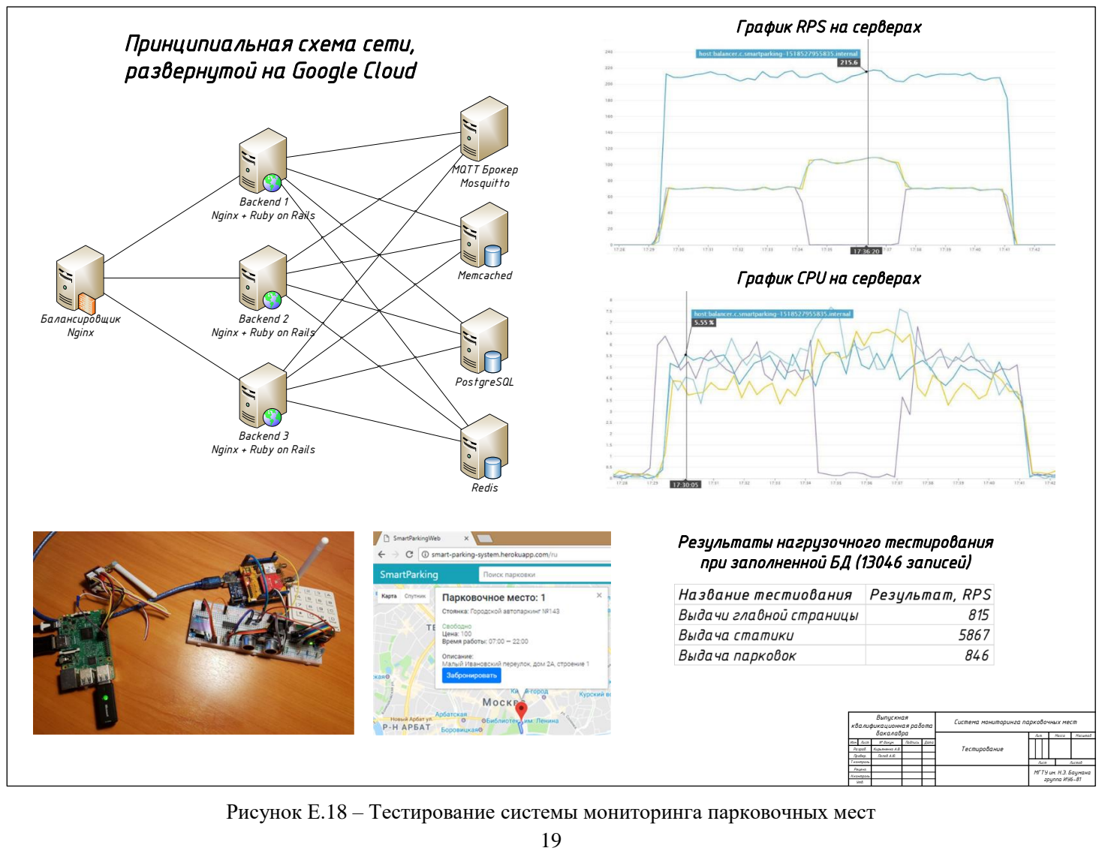
[picture p73: page 19]
Утв.; Лит.; Масса; Масштаб; Лист; Листов; Тестирование; Реценз.; МГТУ им. Н.Э. Баумана группа ИУ6-81; Memcached; Балансировщик Nginx; PostgreSQL; Redis

MQTT Брокер Mosquitto

Backend 1 Nginx + Ruby on Rails

График CPU на серверах

Backend 2 Nginx + Ruby on Rails

Backend 3 Nginx + Ruby on Rails

Результаты нагрузочного тестирования при заполненной БД (13046 записей)

Выпускная квалификационная работа бакалавра

Система мониторинга парковочных мест

Изм. Лист | докум. | Подпись | Дата

Разраб. | Кирьяненко А.В.
Провер. | Попов А.Ю.
Т.контроль

Н.контроль

Рисунок Е.18 – Тестирование системы мониторинга парковочных мест
