kiryanenko/SmartParking-sensor/SerialModule.cpp

#include "SerialModule.h"


SerialModule::SerialModule(AbstractReceiveMessageHandler *handler) :
	Driver(handler)
{
}


SerialModule::~SerialModule()
{
}


bool SerialModule::send(const byte *data, size_t size)
{
	Serial.write(static_cast<uint8_t>(size));
	const auto sendedCount = Serial.write(data, size);
	Serial.println();
	return sendedCount == size;
}


bool SerialModule::available()
{
	return Serial.available() > 0;
}


byte* SerialModule::recv(size_t &size)
{
	size = 0;
	const auto len = Serial.read();

	Serial.print(F("[DEBUG] Serial recv, available "));
	Serial.print(Serial.available());
	Serial.print(F(", len = "));
	Serial.println(len);

	if (len <= 0) {
		Serial.print(F("[ERROR] Serial recv: len < 0"));
		return nullptr;
	}

	const auto buf = new uint8_t[len];
	for (; size < len && available(); ++size) {
		buf[size] = Serial.read();
	}

	if (size != len) {
		Serial.print(F("[ERROR] Serial recv: readen count != len; readen count = "));
		Serial.println(size);

		delete[] buf;
		return nullptr;
	}

	return buf;
}
