kiryanenko/SmartParking-sensor/SerialModule.h

#pragma once
#include "Driver.h"


class SerialModule : public Driver
{
public:
	SerialModule(AbstractReceiveMessageHandler *handler);
	~SerialModule();

	bool send(const byte *data, size_t size) override;
	bool available() override;
	byte* recv(size_t &size) override;
};
