kiryanenko/SmartParking-sensor/Display.cpp

#include "Display.h"

#include <ASOLED.h>
#include "MemUtils.h"
#include "Parameters.h"

Display::Display()
{
}


Display::~Display()
{
}

void Display::init()
{
    LD.init();
    LD.clearDisplay();
}

void Display::drawClock()
{
    String timeStr;
    if (hour() < 10) {
        timeStr += '0';
    }
    timeStr += hour();
    timeStr += ':';
    if (minute() < 10) {
        timeStr += '0';
    }
    timeStr += minute();

#ifdef DEBUG
    Serial.print(F("[TIME] "));
    Serial.println(timeStr);
#endif

    LD.printString_6x8(timeStr.c_str(), 98, 7);
}

void Display::showStartPage()
{
    draw();
    LD.printString_6x8(getFlashStr(PSTR("Для оплаты парковки,")), 0, 0);
    LD.printString_6x8(getFlashStr(PSTR("введите 1")), 0, 1);
}

void Display::showEnterParkingPlacePage()
{
    draw();
    LD.printString_6x8(getFlashStr(PSTR("Введите номер")), 0, 0);
    LD.printString_6x8(getFlashStr(PSTR("парковки:")), 0, 1);
    showHelp();
}

void Display::showEnterTimePage()
{
    draw();
    LD.printString_6x8(getFlashStr(PSTR("Введите время (мин):")), 0, 0);
    showHelp();
}

void Display::showPaymentPage(const float cost)
{
    draw();
    LD.printString_6x8(getFlashStr(PSTR("Сумма к оплате:")), 0, 1);
    LD.printNumber(cost, 2, 0, 2);
    LD.printString_6x8(getFlashStr(PSTR("руб")), 109, 2);
    showHelp();
}

void Display::showSuccessPaymentPage(const float change)
{
    draw();
    LD.printString_6x8(getFlashStr(PSTR("Оплата произведена.")), 0, 0);
    LD.printString_6x8(getFlashStr(PSTR("Сдача: ")), 0, 1);
    LD.printNumber(change, 2, 42, 2);
    LD.printString_6x8(getFlashStr(PSTR("руб")), 109, 2);
    LD.printString_6x8(getFlashStr(PSTR("Нажмите любую клавишу")), 0, 6);
}

void Display::showError(const char* error)
{
    draw();
    LD.printString_6x8(getFlashStr(PSTR("Ошибка!")), 0, 0);
    LD.printString_6x8(getFlashStr(error), 0, 1);
    LD.printString_6x8(getFlashStr(PSTR("Нажмите любую клавишу")), 0, 6);
}

void Display::drawInput(String& inputStr)
{
    LD.printString_6x8(getFlashStr(PSTR("                     ")), 0, 3);
    LD.printString_6x8(inputStr.c_str(), (128 - inputStr.length()) / 2 - 1, 3);
}

void Display::draw()
{
    LD.clearDisplay();
    drawClock();
}

void Display::showHelp()
{
    LD.printString_6x8(getFlashStr(PSTR("* - Далее")), 0, 5);
    LD.printString_6x8(getFlashStr(PSTR("# - Отмена")), 0, 6);
}
