kiryanenko/SmartParking-sensor/Timer.h

#pragma once

// Класс таймера
// Может спокойно обработать случай переполнения счетчика времени 
class Timer
{
    unsigned long m_startTime;
    unsigned long m_finishTime;
    bool m_isOverflow;

public:
    explicit Timer();
    ~Timer();

    void start(const unsigned long period);
    bool isFinished() const;
};
